urecheandreea/E-book-Reader/Images/DisplayView.png

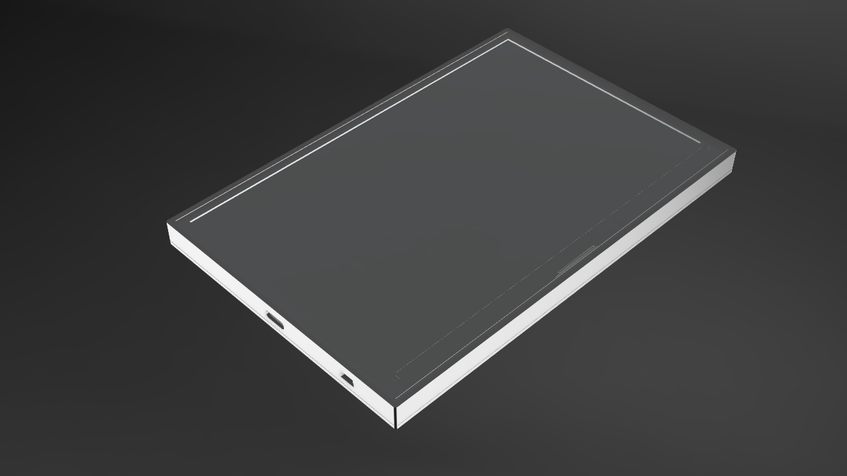
Images/DisplayView.png
