urecheandreea/E-book-Reader/Images/PCBBattery.png

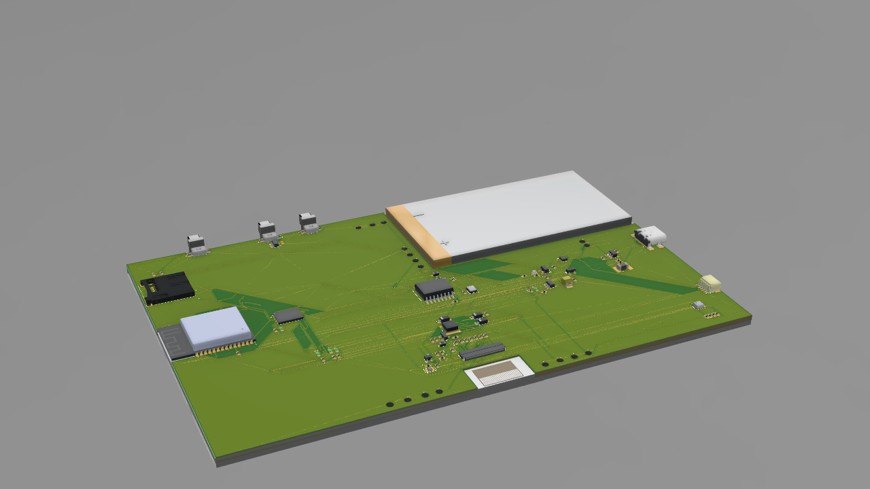
Images/PCBBattery.png
