urecheandreea/E-book-Reader/Images/sideView.png

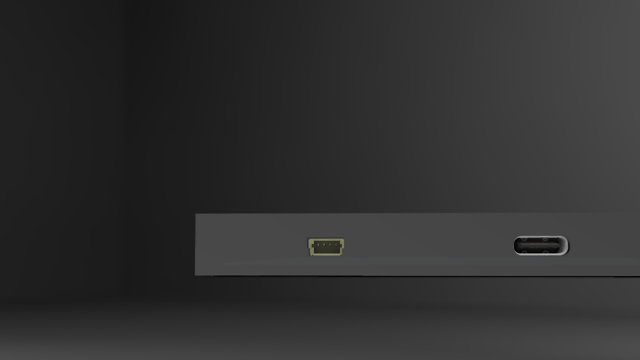
Images/sideView.png
